wolfwood/tryadactyl/fingers.scad

use <assembly.scad>;

strut_mounted_finger_plates(thumb=false);
