wolfwood/tryadactyl/plate.scad

use <assembly.scad>;

base_plate(debug=false);
