wolfwood/tryadactyl/assembly/plate.scad

use <../assembly.scad>;

base_plate(debug=false);
