wolfwood/tryadactyl/assembly/thumb.scad

use <../assembly.scad>;

mounted_thumb();
