wolfwood/tryadactyl/testers/wrapper.scad

/*
 * Used to compare old pre-rendered .stls to the current output
 *  any deviation is a test 'failure'. if the changes are due to intentional
 *  redesign, the old .stl can be replaced.
 */


module invoke_stl(name) {
  import(str("../things/testers/", name, "_tester.stl"));
}

testnamelist="";

module testwrapper(){
  if (!is_undef(testname)) {
    test(testname);
  } else {
    for (testname=testnamelist) {
      test(testname);
    }
  }
}

module test(name) {
  color("red") difference() {
    union() invoke_stl(str("REFERENCE_", name));
    union() invoke_stl(name);
  }

  color("green") difference() {
    invoke_stl(name);
    invoke_stl(str("REFERENCE_", name));
  }
}

testwrapper();
