wolfwood/tryadactyl/key/prerendered/cherry/key.scad

include <../../../KeyV2/includes.scad>

// no stem, we only care about the exterior shape
blank()
cherry_row(row) key();
