wolfwood/tryadactyl/key/prerendered/sa/key.scad

include <../../../KeyV2/includes.scad>

blank()
sa_row(row) key();
