wolfwood/tryadactyl/testers/offset-tester.scad

use <../settings.scad>;
use <../key/cap.scad>;
use <../key/mount.scad>;
use <../column/util.scad>;
use <../column/layout.scad>;


module offset_tester(rows=4, cols=2, keys=false) {
  row_spacing = create_circular_placement([14.5,25,0]);
  col_spacing = create_flat_placement(outerdia()+spacer());
  homerow=2;
  homecol=1;
  profile_rows=effective_rows(rows,homerow);

  tilt=[-5,0,0];
  offsets=[[0,0,0],[0,4,1]];

  placement_params = layout_placement_params(row_spacing=row_spacing, col_spacing=col_spacing, homerow=homerow, homecol=homecol, profile_rows=profile_rows, offsets=offsets, tilt=tilt);

  if ($preview) {
    *#rotate(tilt) translate([0,0,optional_vector_index(row_spacing[2],0,0)[1]])
    scale([col_spacing[2][1]/row_spacing[2][1],1,1])
    sphere($fn=120,r=optional_vector_index(row_spacing[2],0,0)[1]);
    layout_columns(rows=rows, cols=cols, homerow=homerow, homecol=homecol, keys=keys, wells=false,
		   params=placement_params);
  }

  difference(){
    //install_trackpoint(1, 0, row_spacing, col_spacing, profile_rows, homerow, h1=6, h2=6, stem=-.5, up=.5, tilt=[-7,0,0], square_hole=false)
      layout_columns(rows=rows, cols=cols, keys=false,
		     leftwall=true, rightwall=true, topwall=false, bottomwall=false, narrowsides=false, perimeter=true,
		     params=placement_params);

    translate([0,0,-24-40]) cube([500,500,80],true);

    version=2;
    translate([3*outerdia()/2 + 3*spacer()/2 + directional_decoder(wall_extra_room(),0,1) + optional_vector_index(wall_width(),0,0) -.4, -30, -21])
      rotate([90,0,90]) linear_extrude(.5) text(str(profile(), " Offset v",version), size=6);
  }
}

offset_tester(keys=true);
